Inertie-Production/Phone-Controller/Blender/textures/pcb_Cu.png

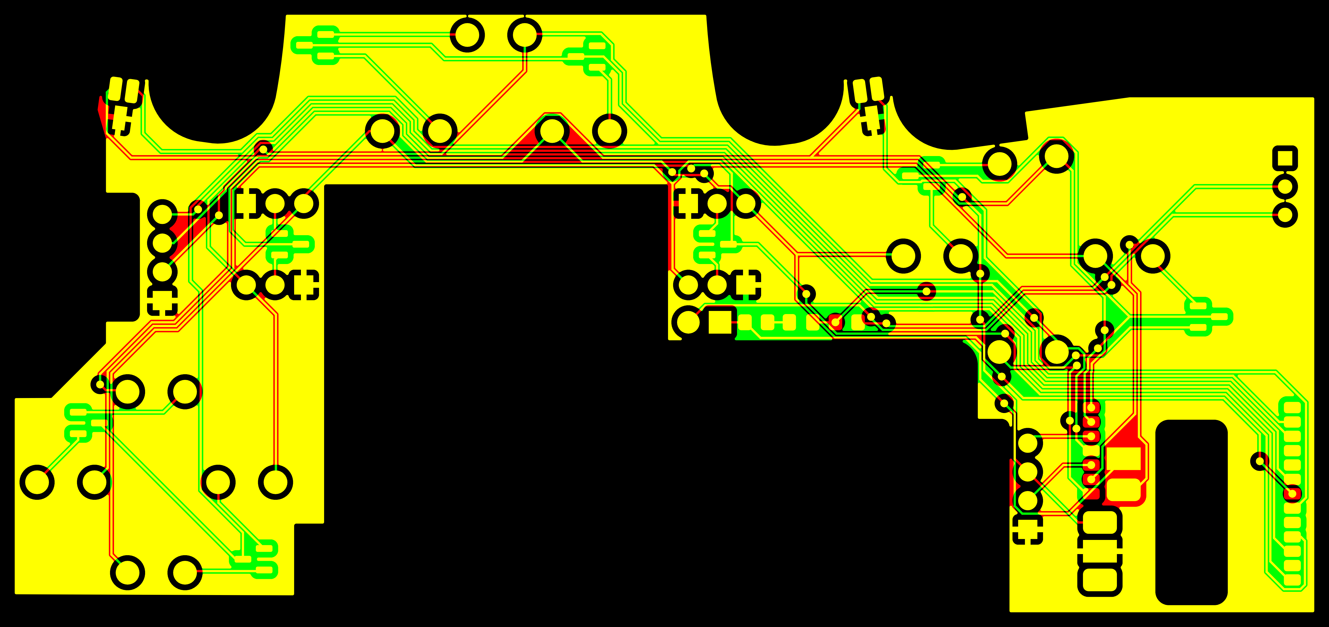
Blender/textures/pcb_Cu.png
