Inertie-Production/Phone-Controller/Blender/textures/pcb_SilkS.png

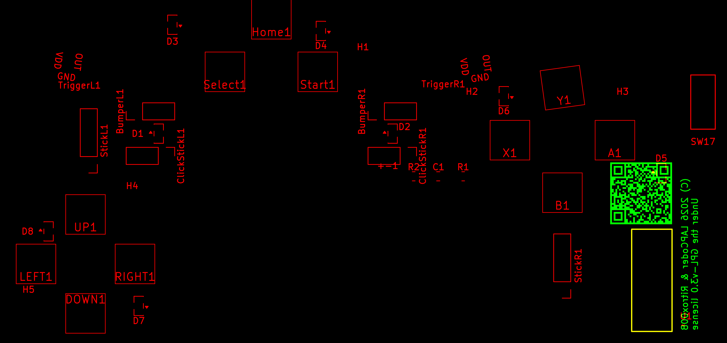
Blender/textures/pcb_SilkS.png
